jernej13/LoRa-Pager/pictures/IMG_20230325_204751.jpg

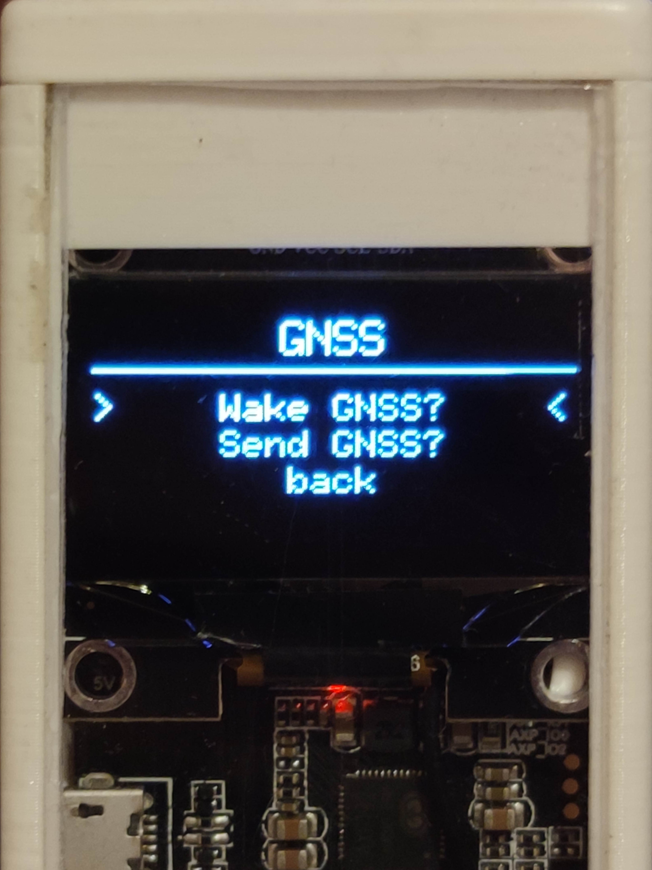
pictures/IMG_20230325_204751.jpg
