jernej13/LoRa-Pager/pictures/IMG_20230325_204828.jpg

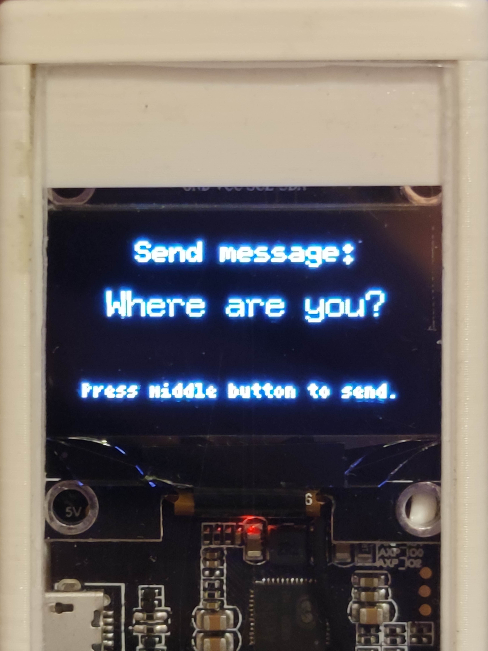
pictures/IMG_20230325_204828.jpg
