jernej13/LoRa-Pager/pictures/IMG_20230326_230949.jpg

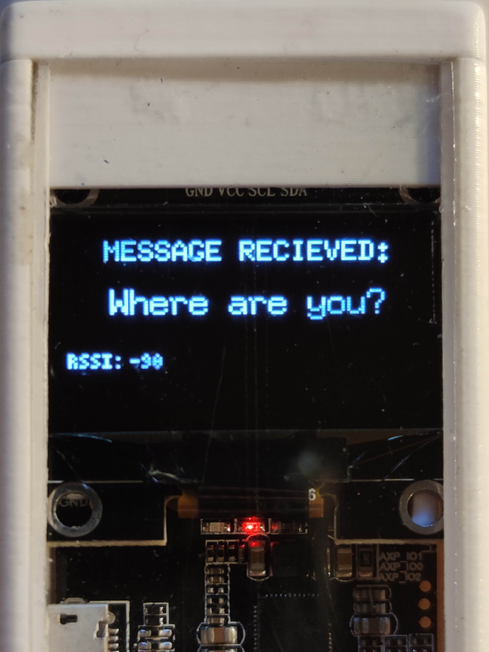
pictures/IMG_20230326_230949.jpg
