jernej13/LoRa-Pager/pictures/IMG_20230327_094044.jpg

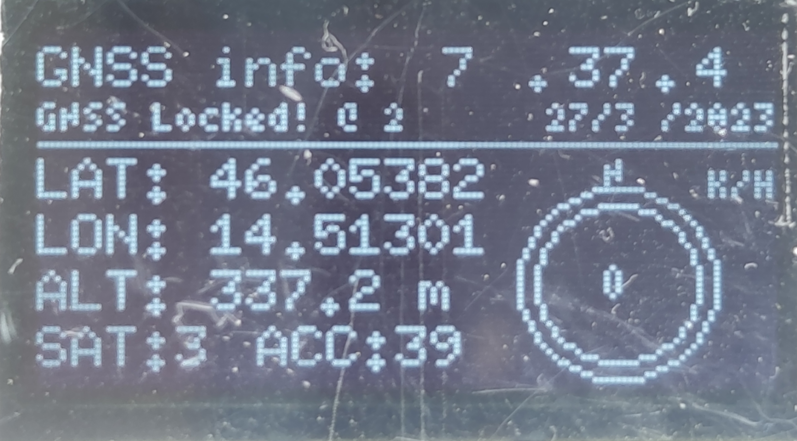
pictures/IMG_20230327_094044.jpg
