jernej13/LoRa-Pager/pictures/IMG_20230327_094235.jpg

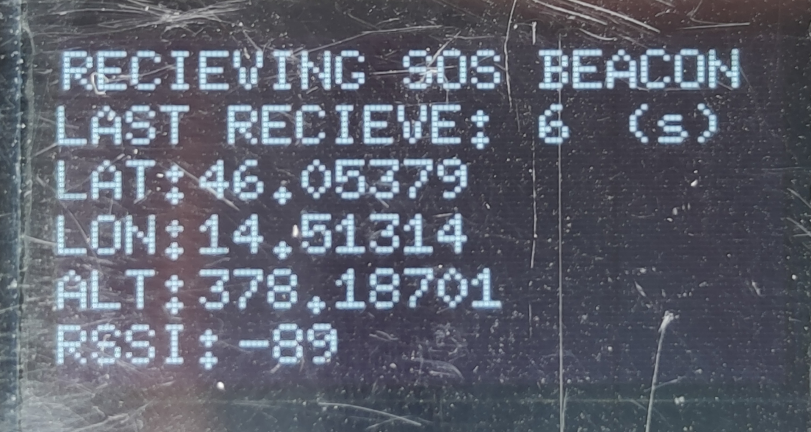
pictures/IMG_20230327_094235.jpg
