jernej13/LoRa-Pager/pictures/IMG_20230327_094317.jpg

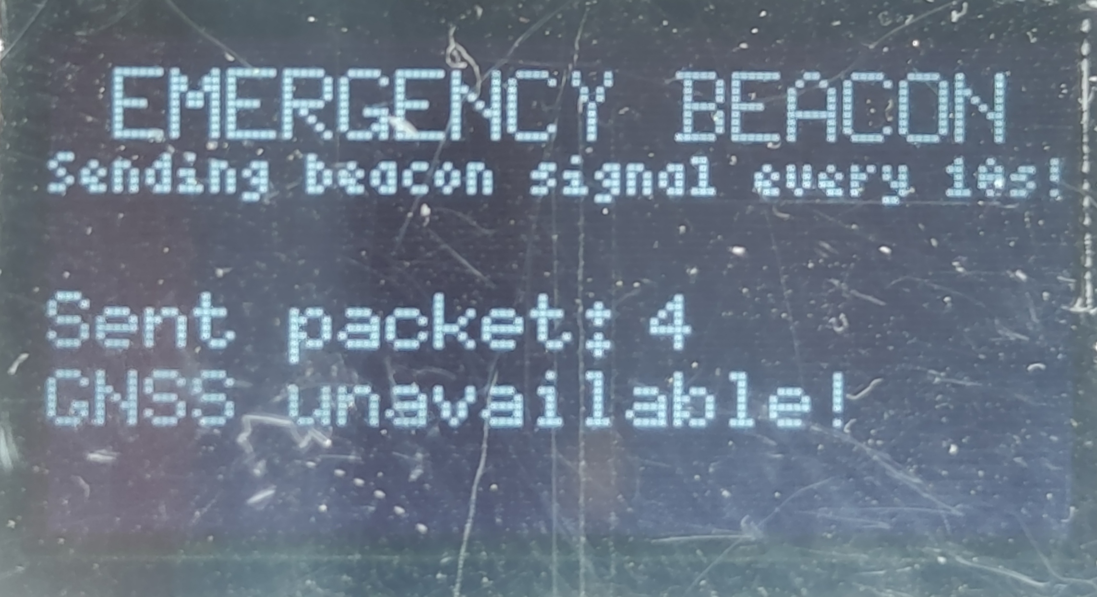
pictures/IMG_20230327_094317.jpg
