jernej13/LoRa-Pager/pictures/IMG_20230327_110351.jpg

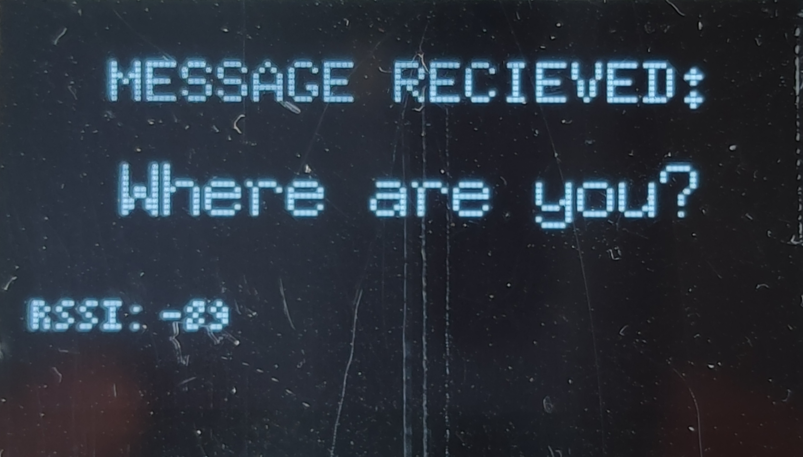
pictures/IMG_20230327_110351.jpg
