jernej13/LoRa-Pager/tests/TEST1/map pic.png

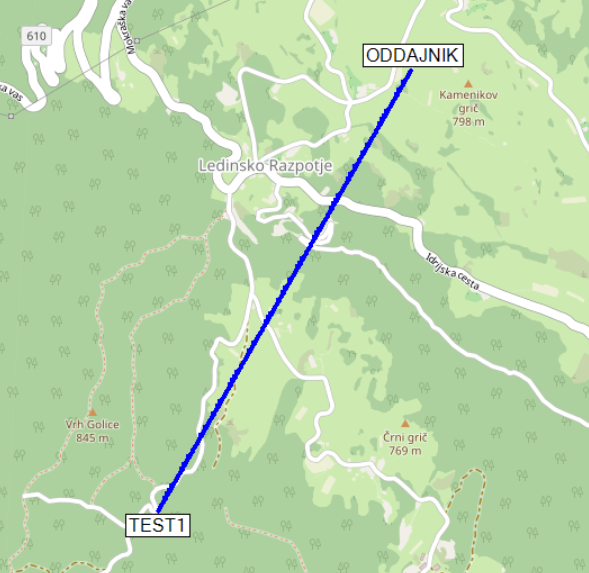
tests/TEST1/map pic.png
