jernej13/LoRa-Pager/tests/TEST3/link pic.png

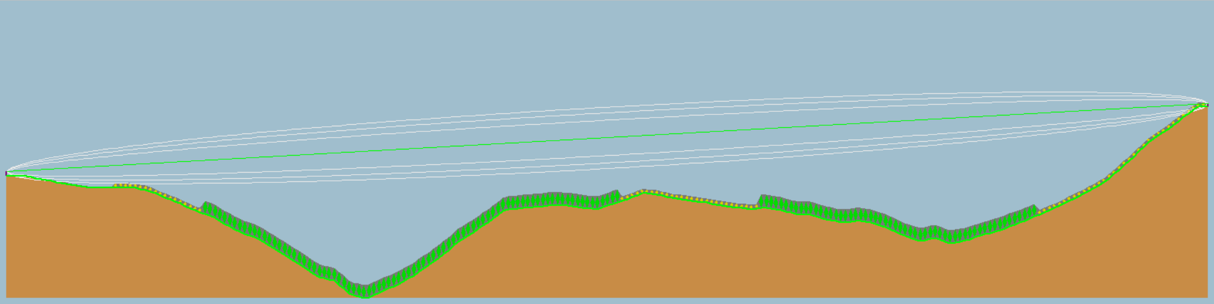
tests/TEST3/link pic.png
