jernej13/LoRa-Pager/tests/TEST3/map pic.png

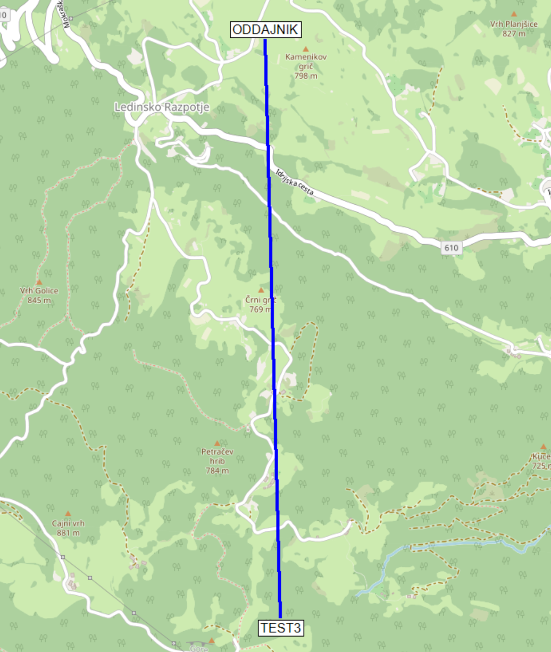
tests/TEST3/map pic.png
