jernej13/LoRa-Pager/tests/TEST4/map pic.png

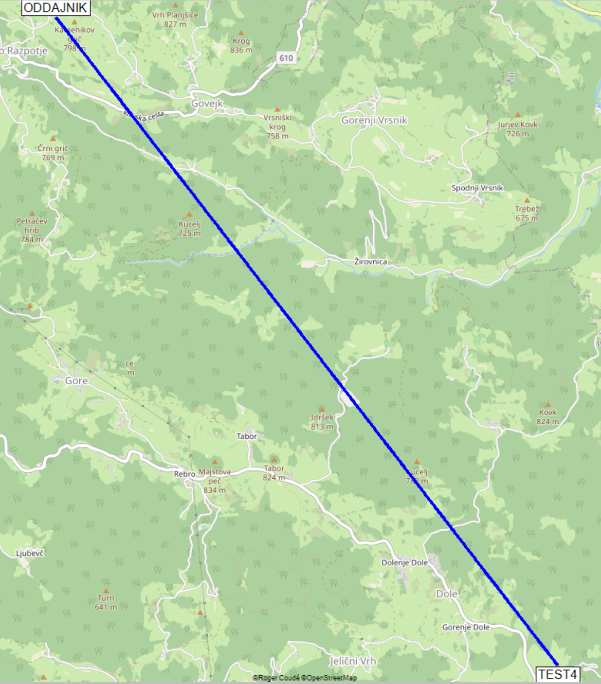
tests/TEST4/map pic.png
