jernej13/LoRa-Pager/schematics/Shema.kicad_sch

## KiCad design schematics/Shema.kicad_sch (2026-03-10)

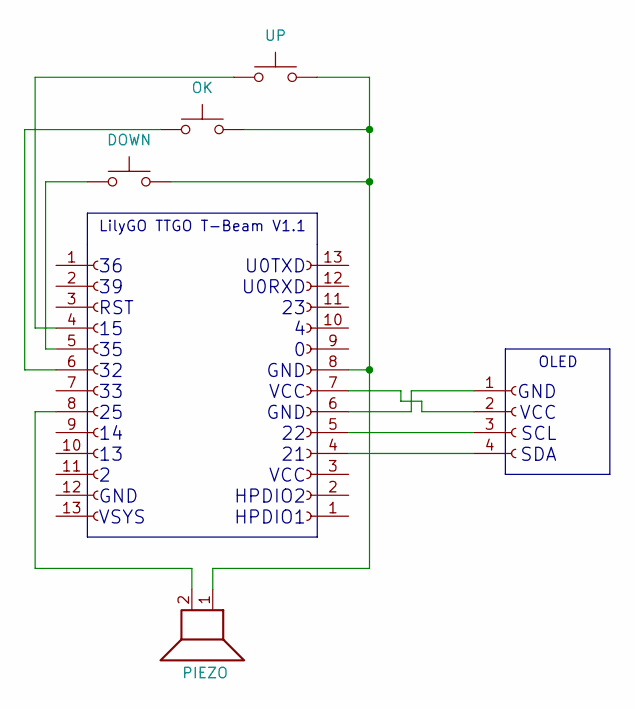
[picture p60: schematic Shema.kicad_sch]

Parts:
DOWN: SW_Push
OK: SW_Push
OLED: Conn_01x04_Female
PIEZO: Speaker
UP: SW_Push

Connections:
unnamed: DOWN.2, OK.2, PIEZO.1, UP.2

Notes on the sheet:
U0TXD U0RXD 23 4 0 GND VCC GND 22 21 VCC HPDIO2 HPDIO1
GND VCC SCL SDA
36 39 RST 15 35 32 33 25 14 13 2 GND VSYS
LilyGO TTGO T-Beam V1.1
OLED
